Echo7394/EcoStat/Case_Models/microstat.png

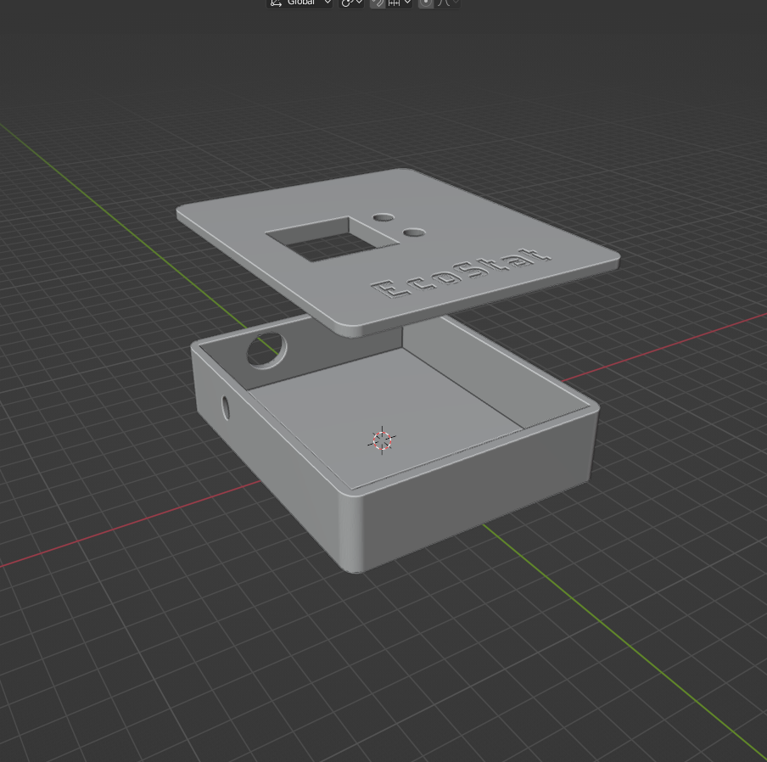
Case_Models/microstat.png
