Echo7394/EcoStat/img/20231014_162400.jpg

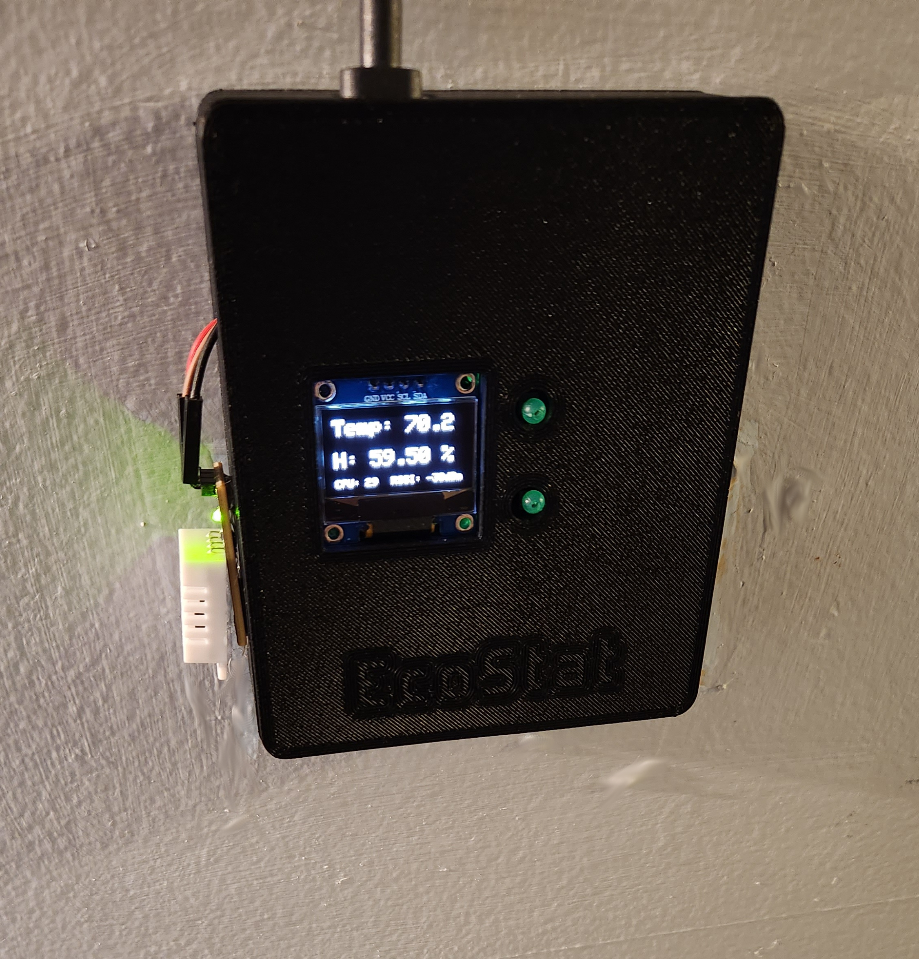
img/20231014_162400.jpg
