Echo7394/EcoStat/img/EN.png

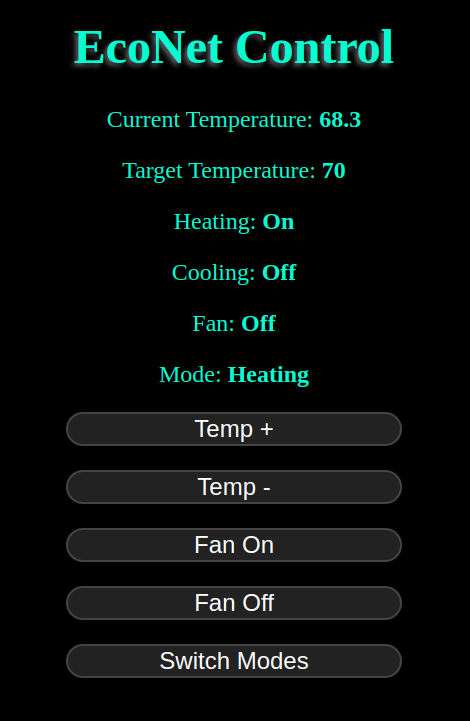
img/EN.png
